altJSV/rgbring/filesystem.ino

void eeprom_read()
{
  //Чтение ssid
  String esid; //временная переменная для хранения ssid
  for (int i = 0; i < 32; ++i)
  {
    esid += char(EEPROM.read(i));
  }
  Serial.println();
  Serial.print("SSID: ");
  Serial.println(esid);
  ssid=esid;//записываем в память прочитанный ssid
  Serial.println("Reading EEPROM pass");
 //чтение пароля
  String epass = "";
  for (int i = 32; i < 96; ++i)
  {
    epass += char(EEPROM.read(i));
  }
  Serial.print("PASS: ");
  Serial.println(epass);
  password=epass; //записываем в память считанный пароль
}

bool eeprom_write(String qsid,String qpass)
{
  if (qsid.length() > 0 && qpass.length() > 0) 
    {
        Serial.println("clearing eeprom");
        for (int i = 0; i < 96; ++i) {
          EEPROM.write(i, 0);
        }
        Serial.println(qsid);
        Serial.println("");
        Serial.println(qpass);
        Serial.println("");
 
        Serial.println("writing eeprom ssid:");
        for (int i = 0; i < qsid.length(); ++i)
        {
          EEPROM.write(i, qsid[i]);
          Serial.print("Wrote: ");
          Serial.println(qsid[i]);
        }
        Serial.println("writing eeprom pass:");
        for (int i = 0; i < qpass.length(); ++i)
        {
          EEPROM.write(32 + i, qpass[i]);
          Serial.print("Wrote: ");
          Serial.println(qpass[i]);
        }
        EEPROM.commit();
        return true;
    } 
    else
    {
      return false;
    }
}
